ducklord/SPINC/PCB/SPINC AA Charger/project_libraries/3D-models/82672Heimdall.step

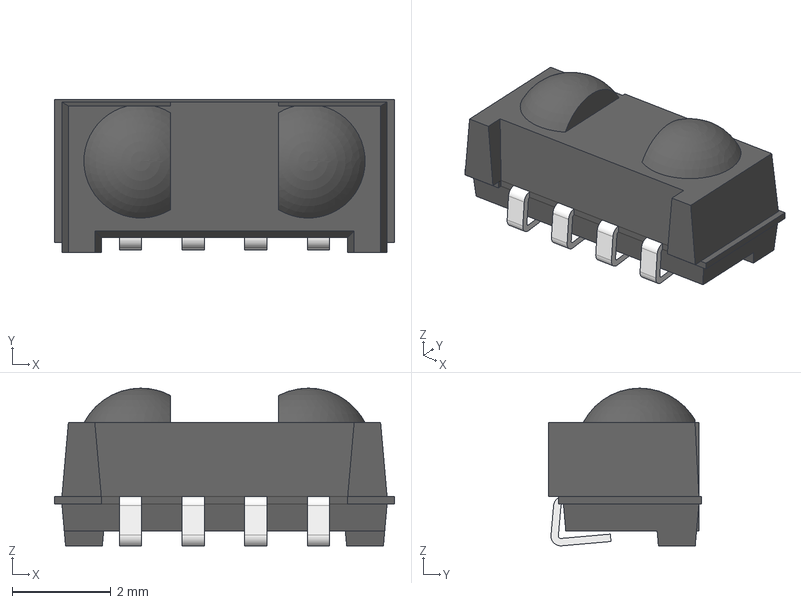
[picture p17: CAD file, 2024-11-08]
PCB/SPINC AA Charger/project_libraries/3D-models/82672Heimdall.step
6.90 x 3.10 x 3.20 mm
