ducklord/SPINC/PCB/SPINC AA Charger/project_libraries/3D-models/68711014022 (rev1).stp

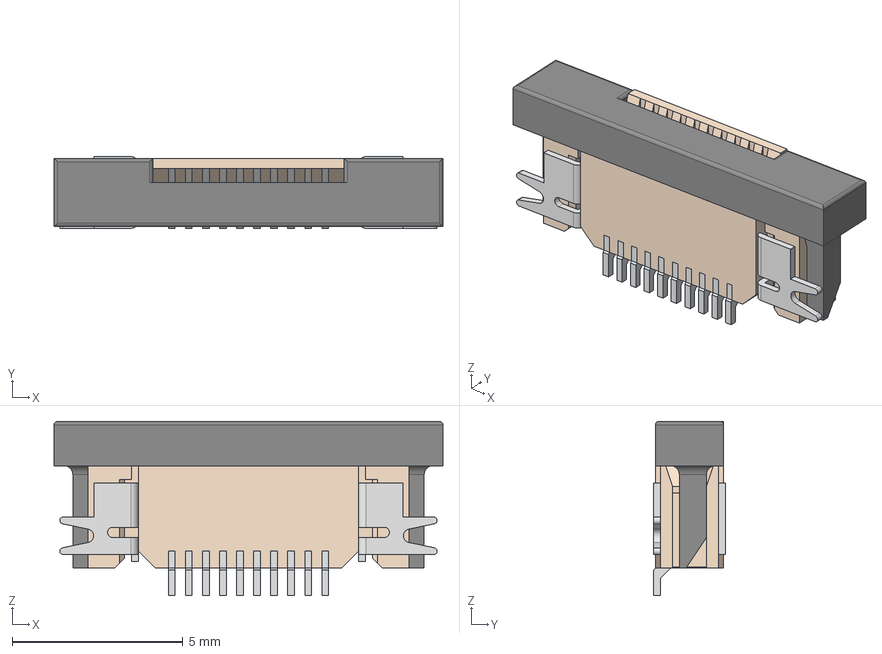
[picture p18: CAD file, 2024-11-08]
PCB/SPINC AA Charger/project_libraries/3D-models/68711014022 (rev1).stp
11.4 x 2.10 x 5.10 mm
6871xx14022_PIN x 10
6871xx14022_Patte
6871xx14022_Patte_2
68711014022_CAP
