ducklord/SPINC/PCB/SPINC AA Charger/project_libraries/3D-models/84352VCNL4040.stp

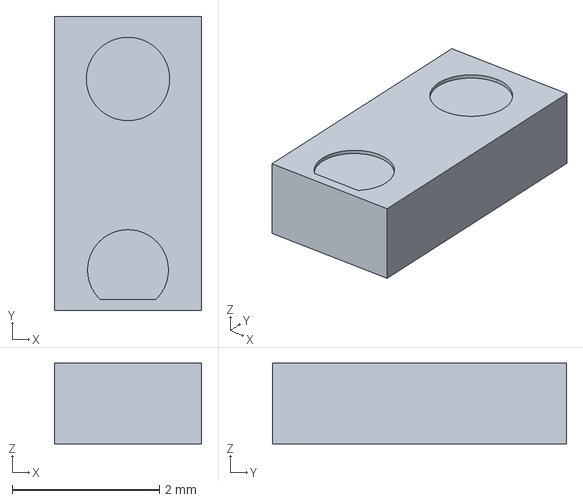
[picture p19: CAD file, 2024-11-08]
PCB/SPINC AA Charger/project_libraries/3D-models/84352VCNL4040.stp
2.00 x 4.00 x 1.10 mm
