ducklord/SPINC/PCB/SPINC AA Charger/project_libraries/3D-models/541325062_colored.step

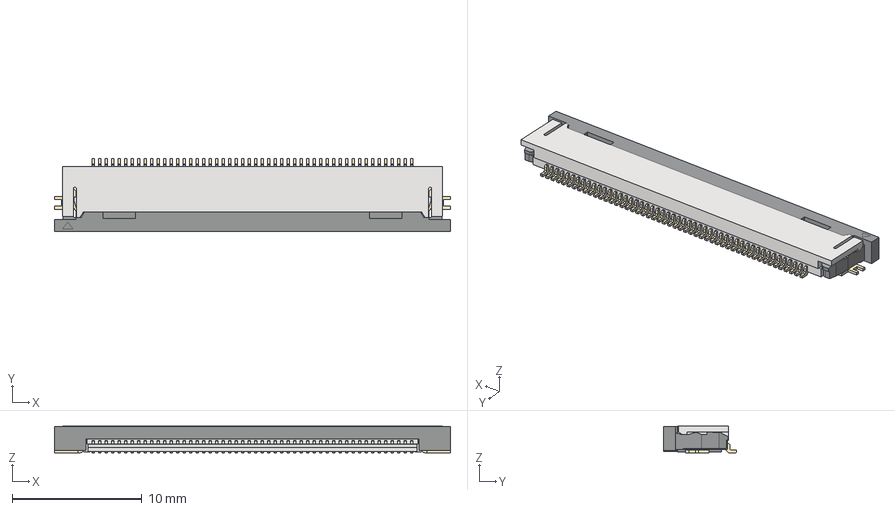
[picture p20: CAD file, 2024-11-08]
PCB/SPINC AA Charger/project_libraries/3D-models/541325062_colored.step
30.5 x 5.60 x 2.05 mm
